MichalAW7/hoovertron/docs/images/infographic2.drawio.png

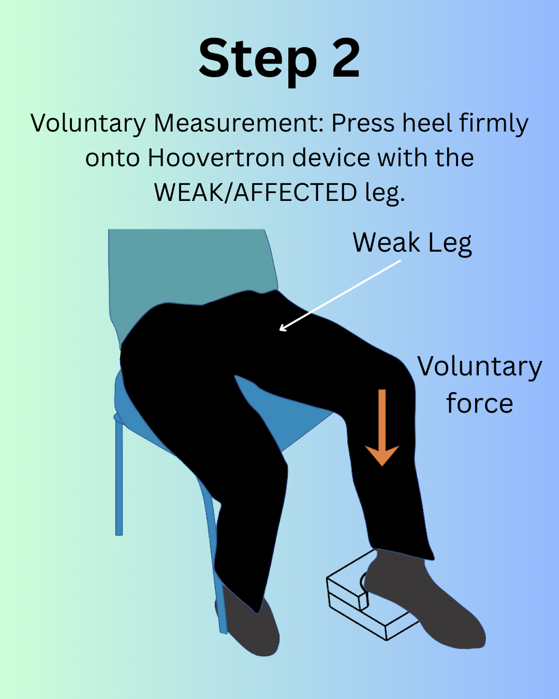
docs/images/infographic2.drawio.png
