MichalAW7/hoovertron/docs/screenshots/step1.png

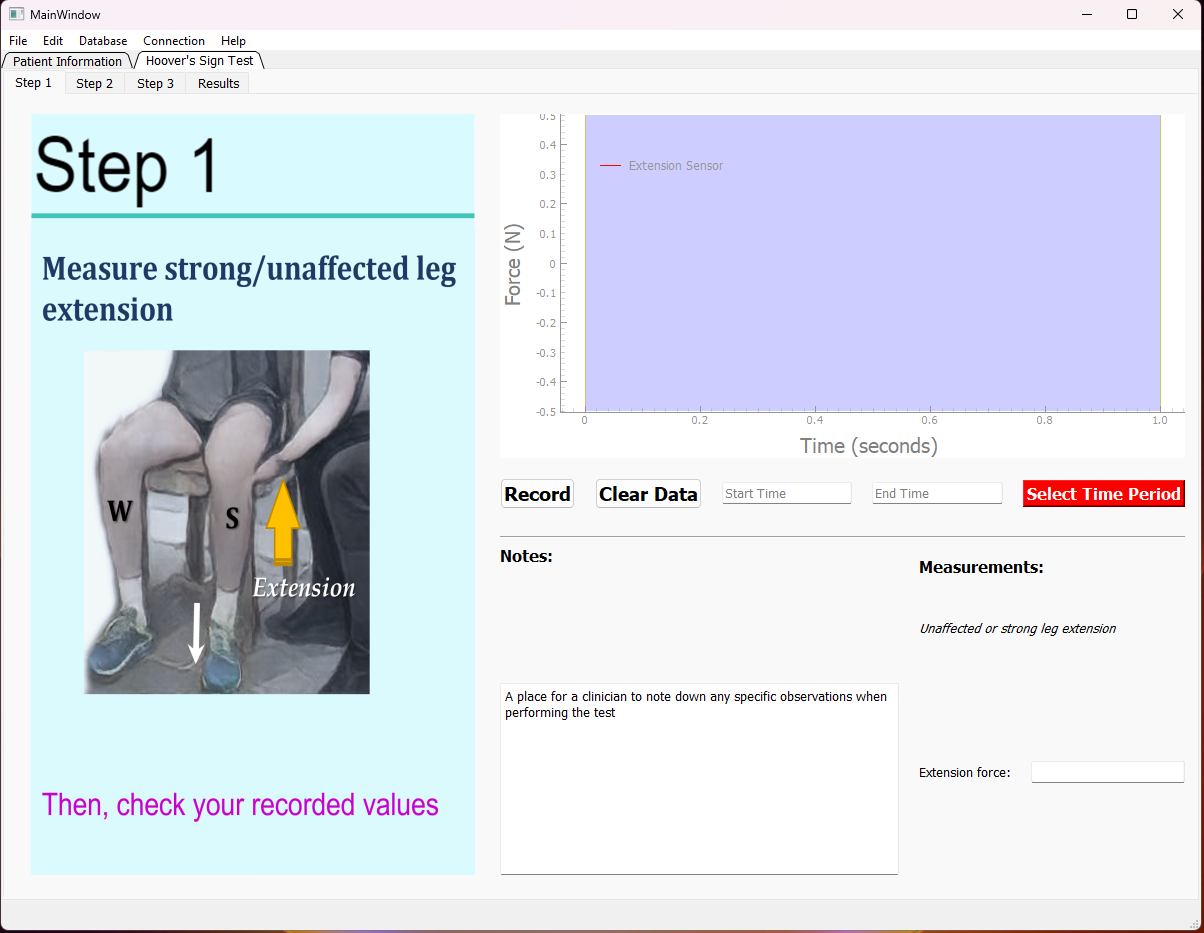
docs/screenshots/step1.png
