MichalAW7/hoovertron/docs/screenshots/step2.png

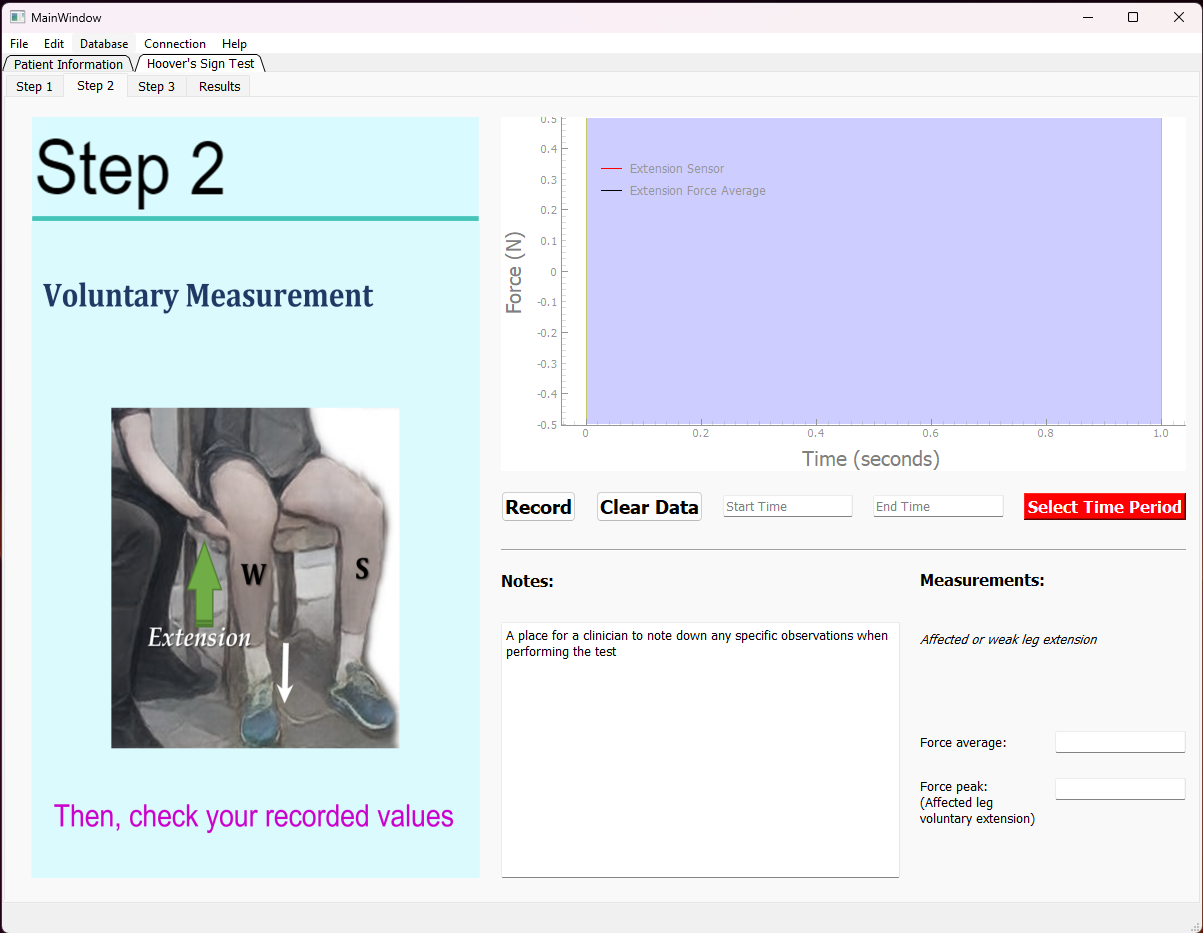
docs/screenshots/step2.png
