MichalAW7/hoovertron/docs/screenshots/step3.png

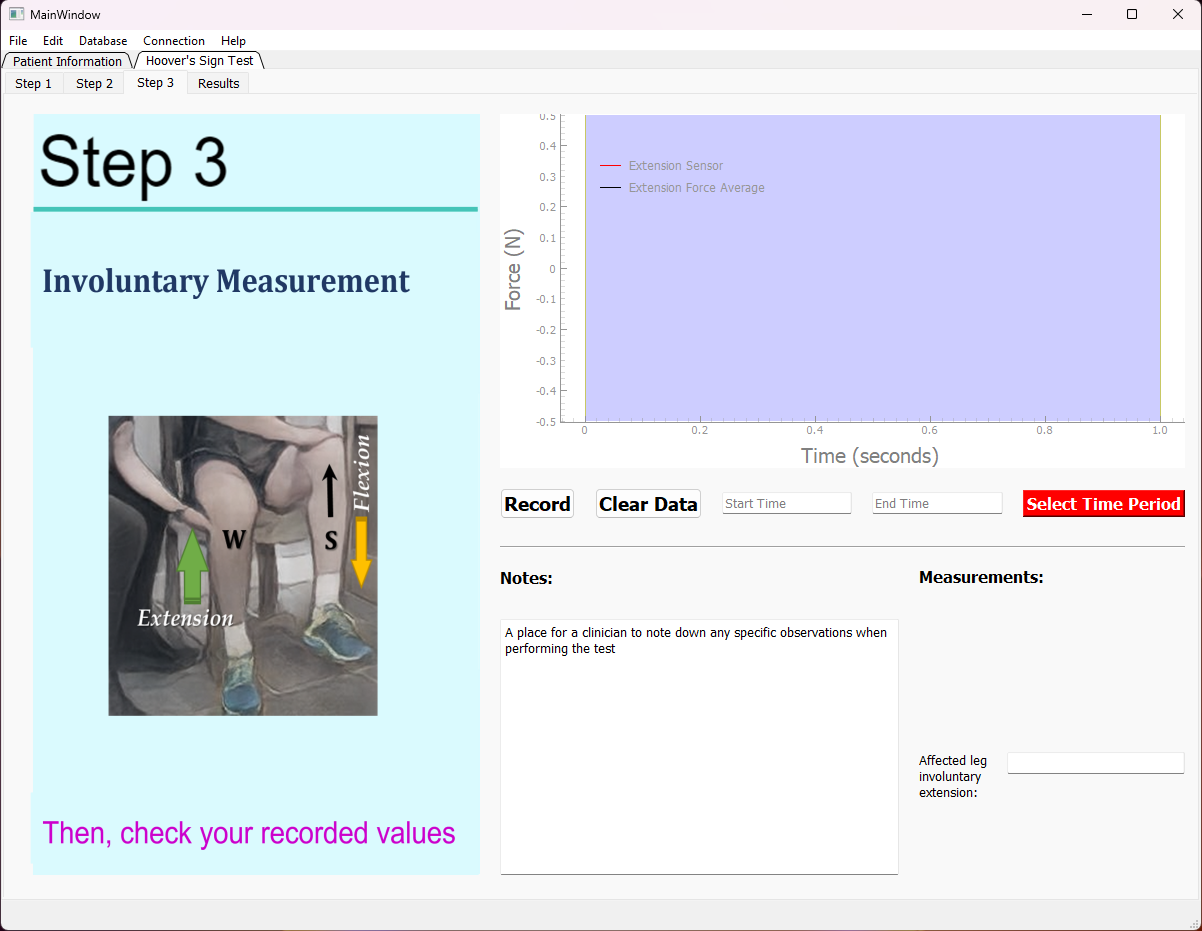
docs/screenshots/step3.png
