MichalAW7/hoovertron/docs/screenshots/results.png

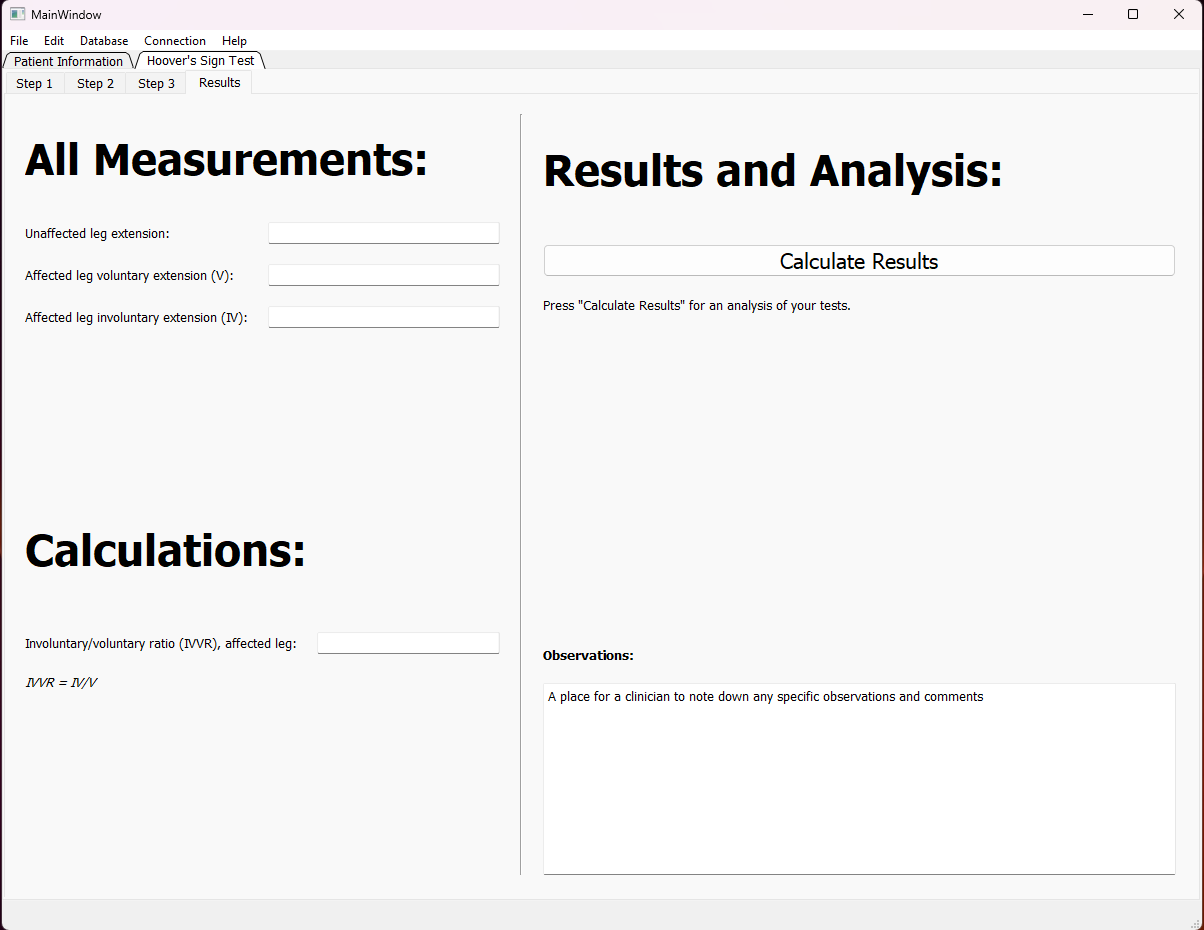
docs/screenshots/results.png
