MichalAW7/hoovertron/software/gui/config.py

# config.py
import os
import sys

CONFIG_FILE_PATH = os.path.join(os.path.expanduser('~'), 'gui_config.ini')

def get_resource_path(relative_path):
    """ Get absolute path to resource, works for dev and for PyInstaller """
    try:
        # PyInstaller creates a temp folder and stores path in _MEIPASS
        base_path = sys._MEIPASS
    except Exception:
        base_path = os.path.abspath(".")

    return os.path.join(base_path, relative_path)
